chriswblake/github-copilot-lamp/docs/gift/copilot-colored.png

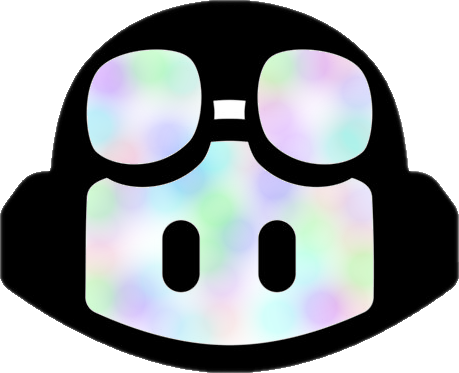
docs/gift/copilot-colored.png
